andygrunwald/things-with-buzzers-hardware/internal/buzzer-setup.graffle/image2.png

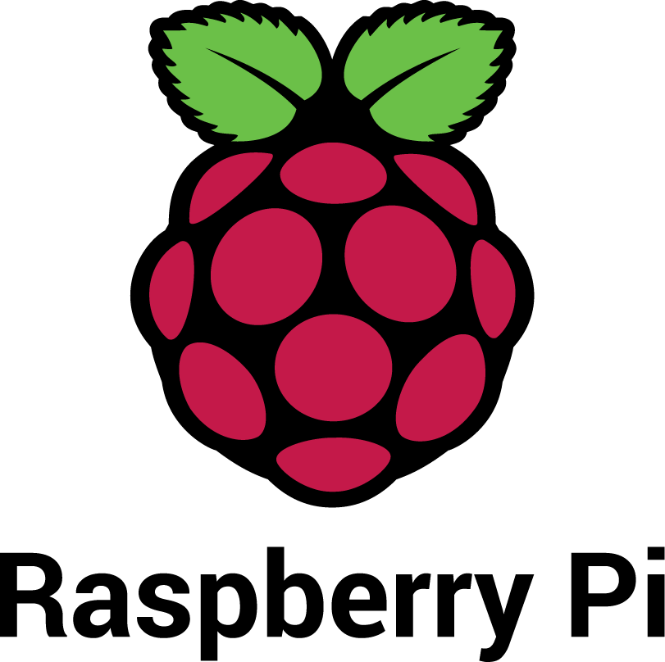
internal/buzzer-setup.graffle/image2.png
