andygrunwald/things-with-buzzers-hardware/internal/buzzer-setup.graffle/image4.png

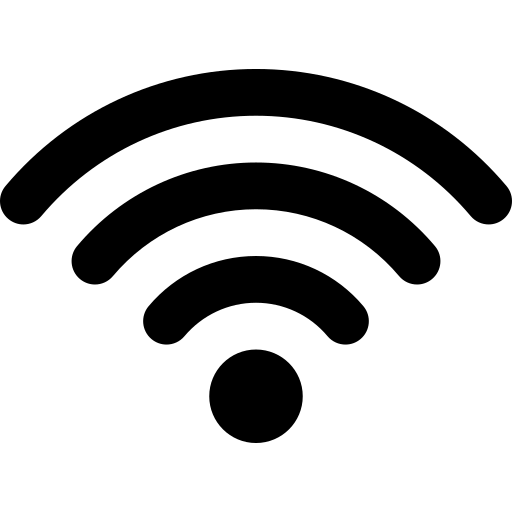
internal/buzzer-setup.graffle/image4.png
